Makerfabs/ESP32-S3-Round-SPI-TFT-with-Touch-1.28/example/LvglBenchmark/img_benchmark_cogwheel_indexed16.c

#include "lv_demo_benchmark.h"

#if LV_USE_DEMO_BENCHMARK

#ifndef LV_ATTRIBUTE_MEM_ALIGN
#define LV_ATTRIBUTE_MEM_ALIGN
#endif

#ifndef LV_ATTRIBUTE_IMG_IMG_COGWHEEL_INDEXED16
#define LV_ATTRIBUTE_IMG_IMG_COGWHEEL_INDEXED16
#endif

const LV_ATTRIBUTE_MEM_ALIGN LV_ATTRIBUTE_IMG_IMG_COGWHEEL_INDEXED16 uint8_t img_benchmark_cogwheel_indexed16_map[] = {
  0x00, 0x00, 0x00, 0x00,   /*Color of index 0*/
  0x6c, 0x5e, 0x4a, 0xff,   /*Color of index 1*/
  0x72, 0x64, 0x50, 0xff,   /*Color of index 2*/
  0x6c, 0x65, 0x5f, 0xff,   /*Color of index 3*/
  0x7b, 0x6b, 0x58, 0xff,   /*Color of index 4*/
  0x82, 0x70, 0x60, 0xff,   /*Color of index 5*/
  0x81, 0x75, 0x68, 0xff,   /*Color of index 6*/
  0x7d, 0x74, 0x72, 0xff,   /*Color of index 7*/
  0x8e, 0x78, 0x67, 0xff,   /*Color of index 8*/
  0x98, 0x81, 0x6e, 0xff,   /*Color of index 9*/
  0x8d, 0x81, 0x73, 0xff,   /*Color of index 10*/
  0x89, 0x81, 0x7d, 0xff,   /*Color of index 11*/
  0xa7, 0x8e, 0x7c, 0xff,   /*Color of index 12*/
  0xa3, 0x96, 0x8b, 0xff,   /*Color of index 13*/
  0x9d, 0x96, 0x92, 0xff,   /*Color of index 14*/
  0xb3, 0x9e, 0x8e, 0xff,   /*Color of index 15*/

  0x00, 0x00, 0x00, 0x00, 0x00, 0x00, 0x00, 0x00, 0x00, 0x00, 0x00, 0x00, 0x00, 0x00, 0x00, 0x00, 0x00, 0x00, 0x00, 0x00, 0x00, 0x00, 0x00, 0xf9, 0x88, 0x88, 0x90, 0x00, 0x00, 0x00, 0x00, 0x00, 0x00, 0x00, 0x00, 0x00, 0x00, 0x00, 0x00, 0x00, 0x00, 0x00, 0x00, 0x00, 0x00, 0x00, 0x00, 0x00, 0x00, 0x00,
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
};

const lv_img_dsc_t img_benchmark_cogwheel_indexed16 = {
  .header.always_zero = 0,
  .header.w = 100,
  .header.h = 100,
  .data_size = 5064,
  .header.cf = LV_IMG_CF_INDEXED_4BIT,
  .data = img_benchmark_cogwheel_indexed16_map,
};

#endif
