Makerfabs/ESP32-S3-Round-SPI-TFT-with-Touch-1.28/example/BoatGauges/BoatGauges.ino

/*
Modify from :https://github.com/VolosR/BoatGauges

*/

#include <TFT_eSPI.h>
#include <CST816S.h>
#include "gauge1.h"
#include "gauge2.h"
#include "gauge3.h"
#include "gauge4.h"
#include "gauge5.h"
#include "gauge6.h"
#include "font.h"

// AUTO MODE 0 USE finger touch screen to change arrow position
#define AUTO_MODE 1

#define ADC_INPUT_PIN 18
#define BUTTON_PIN 17

#define TOUCH_INT 40
#define TOUCH_SDA 38
#define TOUCH_SCL 39
#define TOUCH_RST 16

TFT_eSPI tft = TFT_eSPI();
TFT_eSprite img = TFT_eSprite(&tft);
TFT_eSprite ln = TFT_eSprite(&tft);

CST816S touch(TOUCH_SDA, TOUCH_SCL, TOUCH_RST, TOUCH_INT);

double rad = 0.01745;
int angle;

int sx = 120;
int sy = 120;
int r = 76;

float x[360];
float y[360];
float x2[360];
float y2[360];

const int pwmFreq = 5000;
const int pwmResolution = 8;
const int pwmLedChannelTFT = 0;

int chosenOne = 0;
int minValue[6] = {0, 20, 0, 0, 0, 80};
int maxValue[6] = {40, 100, 60, 80, 70, 160};

int a1, a2;
int result = 0;

void setup()
{
  USBSerial.begin(115200);
  touch.begin();

  ledcSetup(pwmLedChannelTFT, pwmFreq, pwmResolution);
  ledcAttachPin(5, pwmLedChannelTFT);
  ledcWrite(pwmLedChannelTFT, 90);

  pinMode(BUTTON_PIN, INPUT_PULLUP);

  tft.init();
  tft.setRotation(0);
  tft.setSwapBytes(true);
  img.setSwapBytes(true);
  tft.fillScreen(TFT_ORANGE);
  img.createSprite(240, 240);

  tft.setPivot(60, 60);
  img.setTextDatum(4);
  img.setTextColor(TFT_BLACK, 0xAD55);
  img.setFreeFont(&Orbitron_Medium_28);

  int i = 0;
  int a = 136;

  while (a != 44)
  {
    x[i] = r * cos(rad * a) + sx;
    y[i] = r * sin(rad * a) + sy;
    x2[i] = (r - 20) * cos(rad * a) + sx;
    y2[i] = (r - 20) * sin(rad * a) + sy;
    i++;
    a++;
    if (a == 360)
      a = 0;
  }

  xTaskCreatePinnedToCore(Task_TFT, "Task_TFT", 20480, NULL, 0, NULL, 0);
  xTaskCreatePinnedToCore(Task_touch, "Task_touch", 10240, NULL, 3, NULL, 1);
}

void loop()
{
}

void Task_TFT(void *pvParameters)
{
  while (1)
  {
    if (chosenOne == 0)
      img.pushImage(0, 0, 240, 240, gauge1);
    if (chosenOne == 1)
      img.pushImage(0, 0, 240, 240, gauge2);
    if (chosenOne == 2)
      img.pushImage(0, 0, 240, 240, gauge3);
    if (chosenOne == 3)
      img.pushImage(0, 0, 240, 240, gauge4);
    if (chosenOne == 4)
      img.pushImage(0, 0, 240, 240, gauge5);
    if (chosenOne == 5)
      img.pushImage(0, 0, 240, 240, gauge6);

    if (chosenOne == 5)
      img.drawFloat(result / 10.00, 2, 120, 114);
    else if (chosenOne == 4)
      img.drawString(String(result * 100), 120, 114);
    else
      img.drawString(String(result), 120, 114);
    // img.drawString(String(analogRead(22)), 30,10,2);

    a1 = angle - 4;
    a2 = angle + 4;

    if (a1 < 0)
      a1 = angle - 4 + 359;
    if (a2 >= 359)
      a2 = angle + 4 - 359;

    if (result <= minValue[chosenOne] + 4)
      img.fillTriangle(x[angle], y[angle], x2[angle], y2[angle], x2[a2 + 2], y2[a2 + 2], TFT_RED);
    else if (result >= maxValue[chosenOne] - 4)
      img.fillTriangle(x[angle], y[angle], x2[a1 - 2], y2[a1 - 2], x2[angle], y2[angle], TFT_RED);
    else
      img.fillTriangle(x[angle], y[angle], x2[a1], y2[a1], x2[a2], y2[a2], TFT_RED);

    img.pushSprite(0, 0);
  }
}

void Task_touch(void *pvParameters)
{

  long runtime_1 = 0;
  long runtime_2 = 0;

  int auto_adc = 0;
  int auto_unit = 3;

  while (1)
  {
    int last_x = -1;
    int last_y = -1;

    if (touch.available())
    {
      last_x = touch.data.x;
      last_y = touch.data.y;

      int t_r = sqrt((120 - last_x) * (120 - last_x) + (120 - last_y) * (120 - last_y));

      if (t_r < 30)
      {
        if ((millis() - runtime_1) > 1000)
        {
          chosenOne++;
          if (chosenOne >= 6)
            chosenOne = 0;

          runtime_1 = millis();
        }

        continue;
      }
      else
      {
        if (AUTO_MODE == 0)
        {
          double temp_rad = atan((last_y - 120.0) / (last_x - 120.0)) * 100;
          // USBSerial.println(last_x);
          // USBSerial.println(last_y);
          // USBSerial.println(temp_rad);

          int fake_adc = 0;

          if (last_x < 120)
            fake_adc = map(temp_rad, -160, 160, 0, 2047);
          else
            fake_adc = map(temp_rad, -160, 160, 2048, 4095);

          result = map(fake_adc, 0, 4095, minValue[chosenOne], maxValue[chosenOne]);
          angle = map(result, minValue[chosenOne], maxValue[chosenOne], 0, 267);
        }
      }
    }

    if (AUTO_MODE == 1)
    {
      if ((millis() - runtime_2) > 1)
      {
        auto_adc += auto_unit;
        if (auto_adc > 4095)
        {
          auto_adc = 4095;
          auto_unit = 0 - auto_unit;
        }
        if (auto_adc < 0)
        {
          auto_adc = 0;
          auto_unit = 0 - auto_unit;
        }

        result = map(auto_adc, 0, 4095, minValue[chosenOne], maxValue[chosenOne]);
        angle = map(result, minValue[chosenOne], maxValue[chosenOne], 0, 267);

        runtime_2 = millis();
      }
    }
  }
}
