Makerfabs/ESP32-S3-Round-SPI-TFT-with-Touch-1.28/example/LvglBenchmark/lv_font_bechmark_montserrat_28_compr_az.c

#include "lv_demo_benchmark.h"

#if LV_USE_DEMO_BENCHMARK


/*******************************************************************************
 * Size: 28 px
 * Bpp: 4
 * Opts:
 ******************************************************************************/

#ifndef LV_FONT_BENCHMARK_MONTSERRAT_28_COMPR_AZ
#define LV_FONT_BENCHMARK_MONTSERRAT_28_COMPR_AZ 1
#endif

#if LV_FONT_BENCHMARK_MONTSERRAT_28_COMPR_AZ

/*-----------------
 *    BITMAPS
 *----------------*/

/*Store the image of the glyphs*/
static LV_ATTRIBUTE_LARGE_CONST const uint8_t gylph_bitmap[] = {
    /* U+20 " " */

    /* U+61 "a" */
    0x0, 0xb, 0xdf, 0x7f, 0xb6, 0x90, 0x3, 0x47,
    0x42, 0x8, 0x0, 0x96, 0xe4, 0x2, 0x50, 0x15,
    0x9a, 0x95, 0x0, 0x33, 0x0, 0x1d, 0x1d, 0x4c,
    0xad, 0x5a, 0x0, 0x80, 0x1, 0xb8, 0x7, 0x89,
    0xc0, 0x48, 0x3, 0xfd, 0xc0, 0x6, 0x0, 0x14,
    0x67, 0x73, 0xfe, 0x90, 0xc, 0xda, 0xe6, 0x22,
    0x0, 0xf0, 0x94, 0x80, 0xd7, 0x7f, 0xe9, 0x0,
    0x94, 0x1, 0x4a, 0x20, 0x1f, 0xb8, 0x0, 0xa0,
    0x1e, 0xe0, 0xb, 0x80, 0x8, 0x1, 0xc4, 0xe0,
    0x12, 0x80, 0x2d, 0x40, 0x2, 0xd8, 0x1, 0x8a,
    0x80, 0x6b, 0xfd, 0xd2, 0x2c, 0x1, 0x97, 0x58,
    0x40, 0x4, 0xdb, 0x40, 0x10,

    /* U+62 "b" */
    0x7f, 0xf1, 0x80, 0x7f, 0xff, 0xc0, 0x3f, 0xf9,
    0x4b, 0x7d, 0xfb, 0x6a, 0x1, 0xf3, 0x65, 0x20,
    0x81, 0x25, 0x69, 0x0, 0x75, 0x98, 0x2c, 0x4b,
    0x88, 0x16, 0x90, 0x6, 0x12, 0xda, 0x76, 0x8e,
    0x60, 0x7, 0x80, 0x77, 0x90, 0x7, 0x4a, 0x81,
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
    0xf, 0xe6, 0x50, 0x50, 0x1e, 0x0, 0xfc, 0x72,
    0x7, 0x54, 0x3, 0x90, 0xf, 0xf, 0x0, 0xe8,
    0x2b, 0x3, 0x28, 0x7, 0x51, 0x5, 0x8, 0x2,
    0x48, 0x28, 0x80, 0x27, 0x40, 0x74, 0x0, 0xde,
    0x0, 0xf0, 0x1, 0xc0, 0x1c, 0x0, 0x71, 0x50,
    0x15, 0x0,

    /* U+79 "y" */
    0xd, 0xfe, 0x0, 0xfe, 0x2f, 0xf3, 0x85, 0x80,
    0xb0, 0x7, 0xeb, 0x0, 0x38, 0x30, 0x85, 0x80,
    0x7c, 0x2c, 0xe, 0x1, 0x48, 0x12, 0x80, 0x7a,
    0x40, 0x12, 0x1, 0x30, 0x2, 0x40, 0x3c, 0xc0,
    0xa2, 0x1, 0xb, 0x1, 0x98, 0x3, 0x30, 0x84,
    0x80, 0x75, 0x80, 0x24, 0x3, 0x58, 0x19, 0x80,
    0x38, 0x94, 0x14, 0x40, 0x8, 0x41, 0x0, 0x1f,
    0x48, 0x2, 0x40, 0x1e, 0x4, 0x80, 0x1f, 0x19,
    0x81, 0xc0, 0x90, 0x2c, 0x3, 0xfa, 0x0, 0xf,
    0x60, 0x2c, 0x1, 0xfc, 0x84, 0x12, 0xc1, 0x20,
    0x1f, 0xf5, 0x80, 0x80, 0x18, 0x3, 0xfe, 0x61,
    0x0, 0x30, 0x80, 0x7f, 0xf0, 0x1c, 0x1, 0x60,
    0x1f, 0xfc, 0x1, 0x60, 0x42, 0x0, 0xf8, 0x40,
    0x34, 0x0, 0x20, 0x3, 0xf7, 0xdb, 0x2d, 0x30,
    0x29, 0x80, 0x7c, 0xc2, 0x93, 0x4a, 0x5, 0x60,
    0x1f, 0x9a, 0x4c, 0x0, 0x51, 0xa2, 0x1, 0xf8,

    /* U+7A "z" */
    0xbf, 0xff, 0xf9, 0x40, 0x3f, 0xf8, 0x3, 0x39,
    0x9f, 0x38, 0x1, 0x10, 0x46, 0x7e, 0x17, 0x2,
    0xa0, 0xf, 0x87, 0xc0, 0x1c, 0x20, 0x1f, 0x51,
    0x5, 0x18, 0x7, 0xd0, 0x80, 0xea, 0x1, 0xf2,
    0x38, 0x24, 0x0, 0x7c, 0x56, 0x3, 0x40, 0x1f,
    0xbc, 0x1, 0xa2, 0x1, 0xf5, 0x10, 0x49, 0x80,
    0x7c, 0xea, 0xc, 0xc0, 0xf, 0x92, 0x0, 0x68,
    0xcf, 0xe1, 0x90, 0x0, 0xe6, 0x7e, 0x93, 0x0,
    0xff, 0xe0, 0x0
};


/*---------------------
 *  GLYPH DESCRIPTION
 *--------------------*/

static const lv_font_fmt_txt_glyph_dsc_t glyph_dsc[] = {
    {.bitmap_index = 0, .adv_w = 0, .box_w = 0, .box_h = 0, .ofs_x = 0, .ofs_y = 0} /* id = 0 reserved */,
    {.bitmap_index = 0, .adv_w = 121, .box_w = 0, .box_h = 0, .ofs_x = 0, .ofs_y = 0},
    {.bitmap_index = 0, .adv_w = 268, .box_w = 14, .box_h = 15, .ofs_x = 1, .ofs_y = 0},
    {.bitmap_index = 93, .adv_w = 306, .box_w = 16, .box_h = 21, .ofs_x = 2, .ofs_y = 0},
    {.bitmap_index = 197, .adv_w = 256, .box_w = 15, .box_h = 15, .ofs_x = 1, .ofs_y = 0},
    {.bitmap_index = 292, .adv_w = 306, .box_w = 16, .box_h = 21, .ofs_x = 1, .ofs_y = 0},
    {.bitmap_index = 399, .adv_w = 274, .box_w = 15, .box_h = 15, .ofs_x = 1, .ofs_y = 0},
    {.bitmap_index = 493, .adv_w = 158, .box_w = 11, .box_h = 21, .ofs_x = 0, .ofs_y = 0},
    {.bitmap_index = 545, .adv_w = 309, .box_w = 16, .box_h = 20, .ofs_x = 1, .ofs_y = -5},
    {.bitmap_index = 685, .adv_w = 305, .box_w = 15, .box_h = 21, .ofs_x = 2, .ofs_y = 0},
    {.bitmap_index = 747, .adv_w = 125, .box_w = 4, .box_h = 21, .ofs_x = 2, .ofs_y = 0},
    {.bitmap_index = 764, .adv_w = 127, .box_w = 9, .box_h = 26, .ofs_x = -3, .ofs_y = -5},
    {.bitmap_index = 810, .adv_w = 276, .box_w = 16, .box_h = 21, .ofs_x = 2, .ofs_y = 0},
    {.bitmap_index = 898, .adv_w = 125, .box_w = 4, .box_h = 21, .ofs_x = 2, .ofs_y = 0},
    {.bitmap_index = 905, .adv_w = 474, .box_w = 26, .box_h = 15, .ofs_x = 2, .ofs_y = 0},
    {.bitmap_index = 1000, .adv_w = 305, .box_w = 15, .box_h = 15, .ofs_x = 2, .ofs_y = 0},
    {.bitmap_index = 1056, .adv_w = 284, .box_w = 16, .box_h = 15, .ofs_x = 1, .ofs_y = 0},
    {.bitmap_index = 1160, .adv_w = 306, .box_w = 16, .box_h = 20, .ofs_x = 2, .ofs_y = -5},
    {.bitmap_index = 1266, .adv_w = 306, .box_w = 16, .box_h = 20, .ofs_x = 1, .ofs_y = -5},
    {.bitmap_index = 1374, .adv_w = 184, .box_w = 9, .box_h = 15, .ofs_x = 2, .ofs_y = 0},
    {.bitmap_index = 1404, .adv_w = 224, .box_w = 14, .box_h = 15, .ofs_x = 0, .ofs_y = 0},
    {.bitmap_index = 1499, .adv_w = 185, .box_w = 11, .box_h = 19, .ofs_x = 0, .ofs_y = 0},
    {.bitmap_index = 1551, .adv_w = 303, .box_w = 15, .box_h = 15, .ofs_x = 2, .ofs_y = 0},
    {.bitmap_index = 1602, .adv_w = 250, .box_w = 17, .box_h = 15, .ofs_x = -1, .ofs_y = 0},
    {.bitmap_index = 1700, .adv_w = 403, .box_w = 25, .box_h = 15, .ofs_x = 0, .ofs_y = 0},
    {.bitmap_index = 1855, .adv_w = 247, .box_w = 16, .box_h = 15, .ofs_x = 0, .ofs_y = 0},
    {.bitmap_index = 1953, .adv_w = 250, .box_w = 17, .box_h = 20, .ofs_x = -1, .ofs_y = -5},
    {.bitmap_index = 2081, .adv_w = 233, .box_w = 13, .box_h = 15, .ofs_x = 1, .ofs_y = 0}
};

/*---------------------
 *  CHARACTER MAPPING
 *--------------------*/



/*Collect the unicode lists and glyph_id offsets*/
static const lv_font_fmt_txt_cmap_t cmaps[] =
{
    {
        .range_start = 32, .range_length = 1, .glyph_id_start = 1,
        .unicode_list = NULL, .glyph_id_ofs_list = NULL, .list_length = 0, .type = LV_FONT_FMT_TXT_CMAP_FORMAT0_TINY
    },
    {
        .range_start = 97, .range_length = 26, .glyph_id_start = 2,
        .unicode_list = NULL, .glyph_id_ofs_list = NULL, .list_length = 0, .type = LV_FONT_FMT_TXT_CMAP_FORMAT0_TINY
    }
};

/*-----------------
 *    KERNING
 *----------------*/


/*Map glyph_ids to kern left classes*/
static const uint8_t kern_left_class_mapping[] =
{
    0, 0, 1, 2, 3, 4, 5, 6,
    0, 1, 0, 0, 7, 4, 1, 1,
    2, 2, 8, 9, 10, 11, 0, 12,
    12, 13, 12, 14
};

/*Map glyph_ids to kern right classes*/
static const uint8_t kern_right_class_mapping[] =
{
    0, 0, 1, 2, 3, 3, 3, 0,
    3, 2, 4, 5, 2, 2, 4, 4,
    3, 4, 3, 4, 6, 7, 8, 9,
    9, 10, 9, 11
};

/*Kern values between classes*/
static const int8_t kern_class_values[] =
{
    0, 0, 1, 0, 0, 0, 0, 0,
    -4, 0, 0, -2, 0, 0, 0, 0,
    0, 0, 0, -7, -8, -4, 0, -3,
    -4, 0, 0, 0, 3, 0, -3, -8,
    -3, 0, 0, 0, 0, 0, 0, 6,
    0, 0, 0, 0, -7, 0, 0, 0,
    0, 0, 0, 0, -4, -7, -2, -4,
    0, -4, 36, 19, 0, 0, 0, 4,
    0, 0, -4, 0, -10, -3, 0, -8,
    0, -4, -13, -9, -5, 0, 0, 0,
    0, 22, 0, 0, 0, 0, 0, 0,
    -4, -3, -5, -3, 0, -1, 7, 0,
    7, -3, 0, 0, 0, 0, 0, 0,
    0, 0, 0, -4, -4, 0, 0, 0,
    -8, 0, 0, 0, -6, 0, -4, 0,
    0, -8, 0, -7, 0, -7, -3, 7,
    0, -4, -13, -4, -4, 0, -8, 0,
    3, -4, 0, -4, -13, 0, -4, 0,
    0, -4, 0, 0, 0, 1, 0, -4,
    -4, 0
};


/*Collect the kern class' data in one place*/
static const lv_font_fmt_txt_kern_classes_t kern_classes =
{
    .class_pair_values   = kern_class_values,
    .left_class_mapping  = kern_left_class_mapping,
    .right_class_mapping = kern_right_class_mapping,
    .left_class_cnt      = 14,
    .right_class_cnt     = 11,
};

/*--------------------
 *  ALL CUSTOM DATA
 *--------------------*/

/*Store all the custom data of the font*/
static lv_font_fmt_txt_dsc_t font_dsc = {
    .glyph_bitmap = gylph_bitmap,
    .glyph_dsc = glyph_dsc,
    .cmaps = cmaps,
    .kern_dsc = &kern_classes,
    .kern_scale = 16,
    .cmap_num = 2,
    .bpp = 4,
    .kern_classes = 1,
    .bitmap_format = 1
};


/*-----------------
 *  PUBLIC FONT
 *----------------*/

/*Initialize a public general font descriptor*/
lv_font_t lv_font_benchmark_montserrat_28_compr_az = {
    .get_glyph_dsc = lv_font_get_glyph_dsc_fmt_txt,    /*Function pointer to get glyph's data*/
    .get_glyph_bitmap = lv_font_get_bitmap_fmt_txt,    /*Function pointer to get glyph's bitmap*/
    .line_height = 26,          /*The maximum line height required by the font*/
    .base_line = 5,             /*Baseline measured from the bottom of the line*/
#if !(LVGL_VERSION_MAJOR == 6 && LVGL_VERSION_MINOR == 0)
    .subpx = LV_FONT_SUBPX_NONE,
#endif
    .dsc = &font_dsc           /*The custom font data. Will be accessed by `get_glyph_bitmap/dsc` */
};

#endif /*#if LV_FONT_BENCHMARK_MONTSERRAT_28_COMPR_AZ*/

#endif
